Tecsmith/vr61-keyboard-pcb/docs/ref_pcb_dims/GH60_dims.png

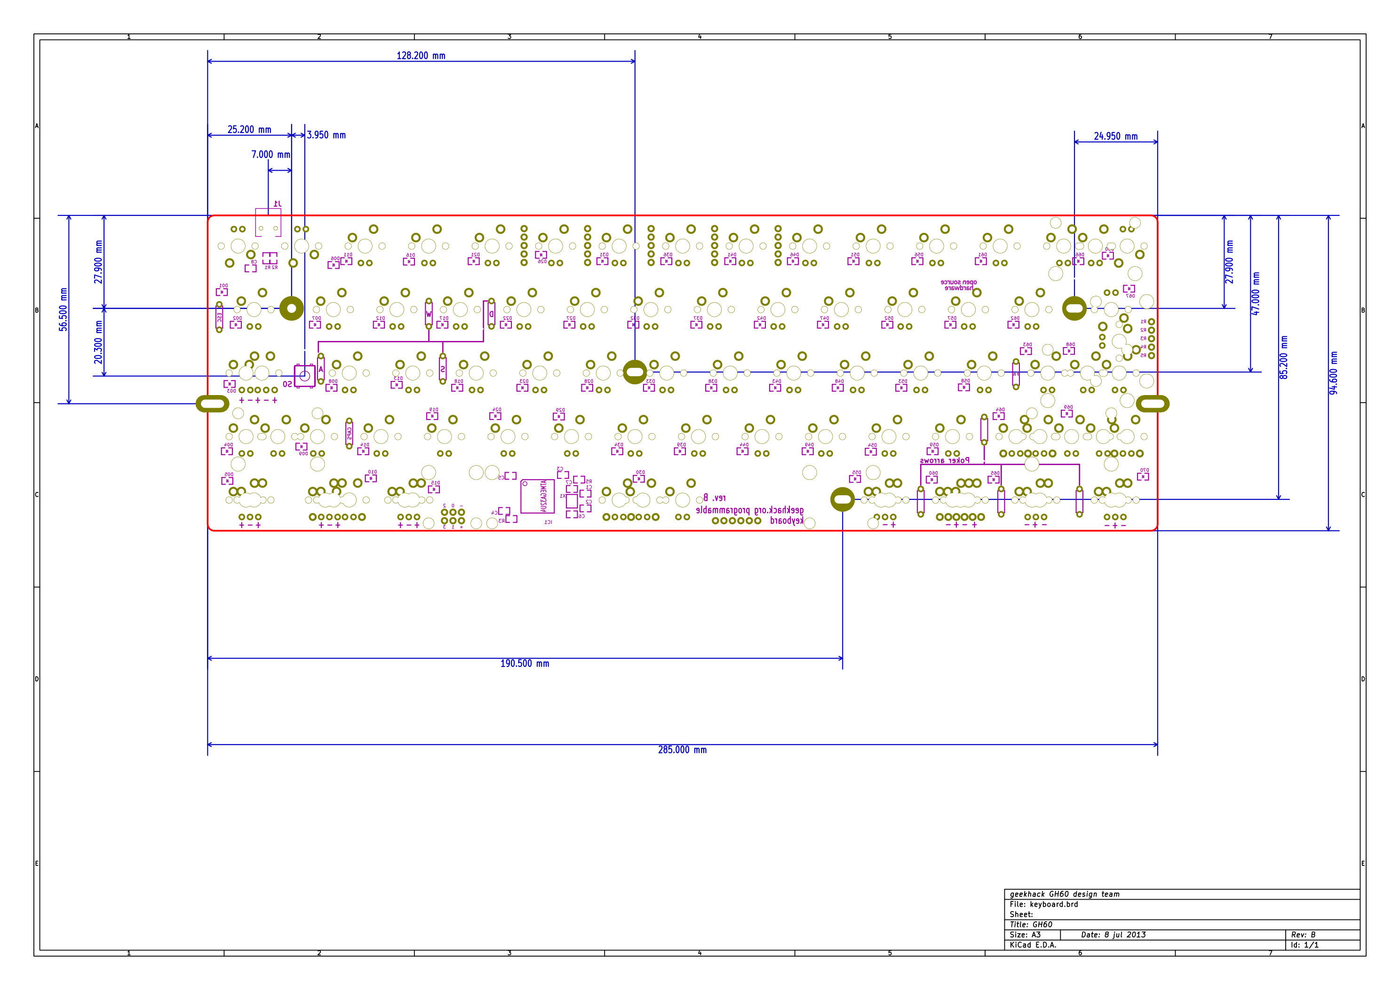
docs/ref_pcb_dims/GH60_dims.png
