Tecsmith/vr61-keyboard-pcb/docs/ref_pcb_dims/gh_60_dimensions.png

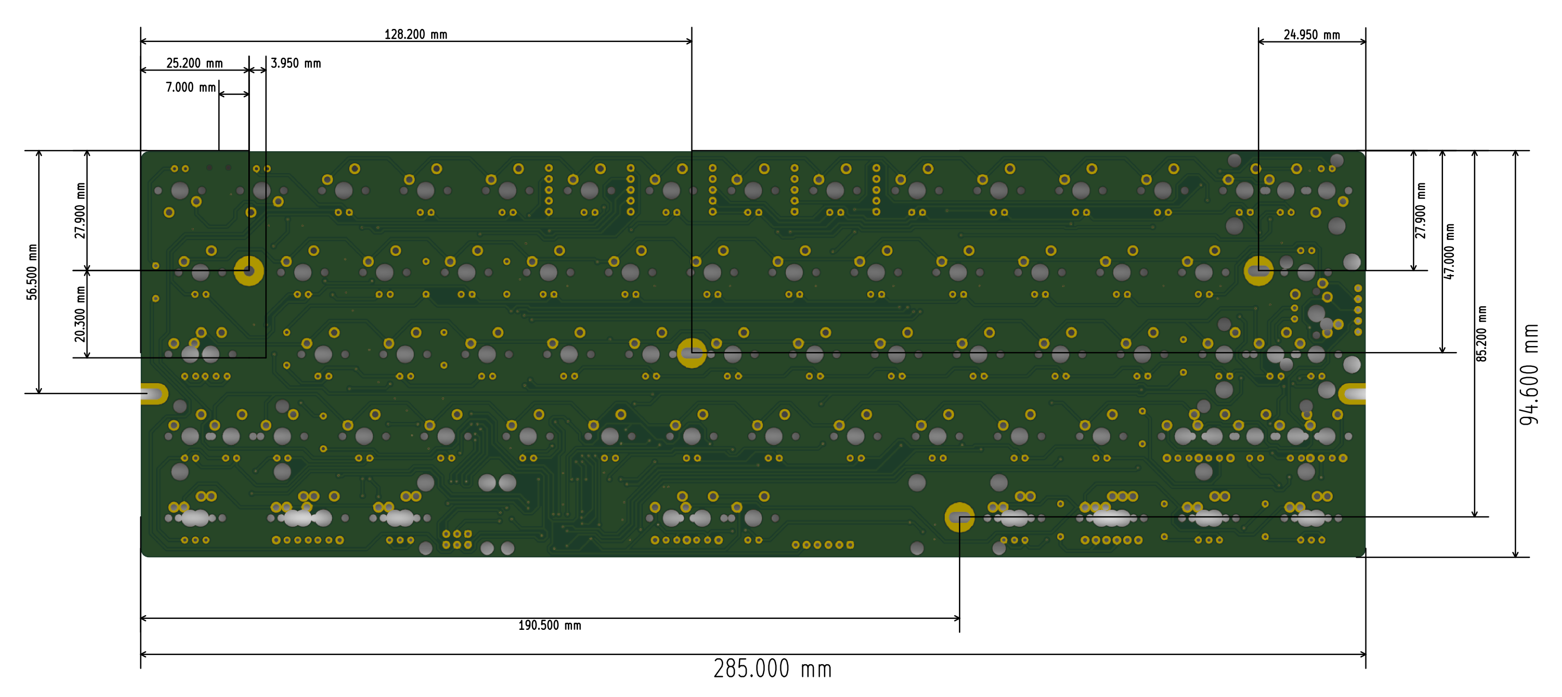
docs/ref_pcb_dims/gh_60_dimensions.png
