Tecsmith/vr61-keyboard-pcb/docs/ref_pcb_dims/mx-switch-dimension-pcb-footprint.jpg

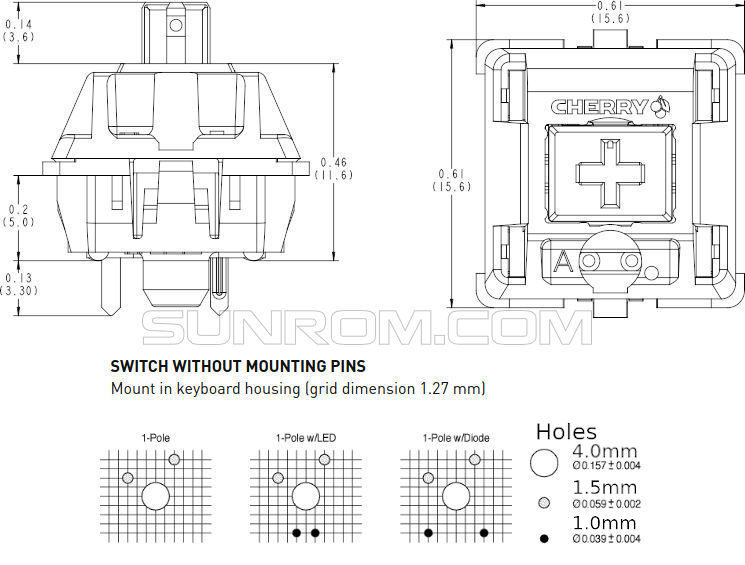
docs/ref_pcb_dims/mx-switch-dimension-pcb-footprint.jpg
