Tecsmith/vr61-keyboard-pcb/docs/ref_pcb_dims/stabilizer_attach.png

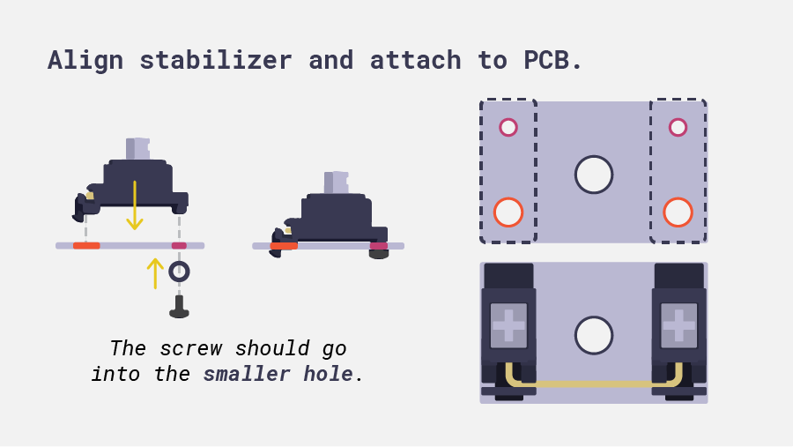
docs/ref_pcb_dims/stabilizer_attach.png
