Tecsmith/vr61-keyboard-pcb/docs/sparkfun_stm32/STM32MicroMod-GraphicalDatasheet.png

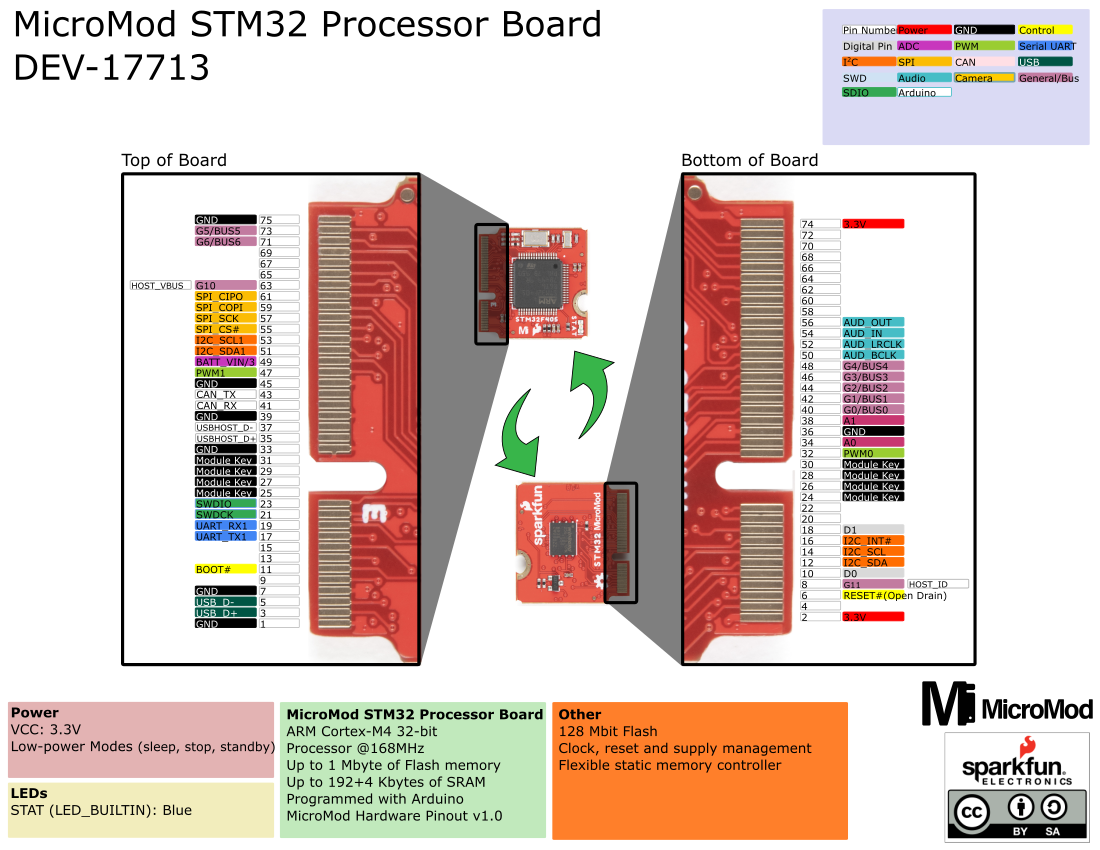
docs/sparkfun_stm32/STM32MicroMod-GraphicalDatasheet.png
