Tecsmith/vr61-keyboard-pcb/kle/vr61-micromod-poker.png

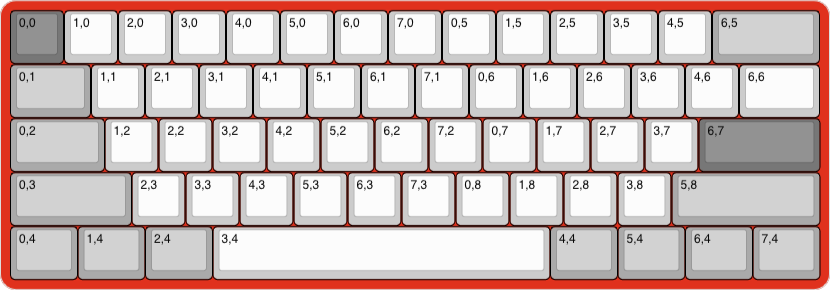
kle/vr61-micromod-poker.png
