Tecsmith/vr61-keyboard-pcb/docs/good_design_arb/3.3v protect and measure.png

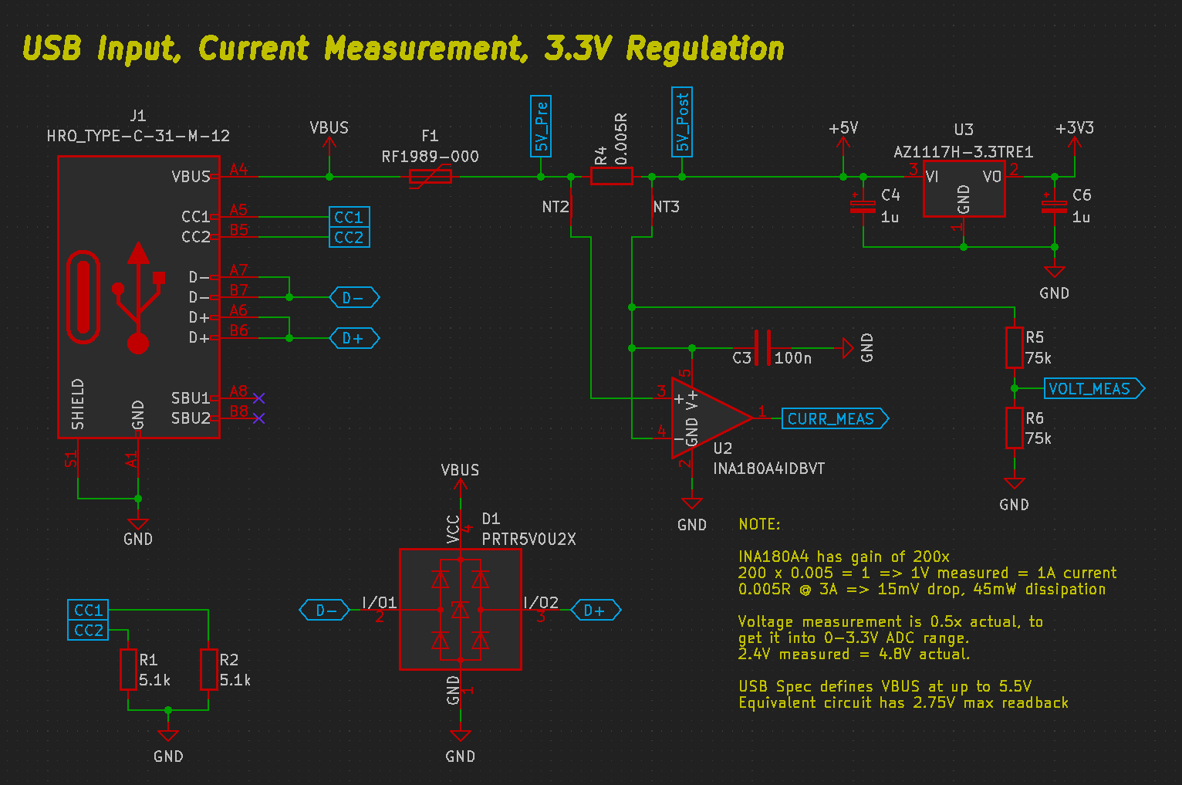
docs/good_design_arb/3.3v protect and measure.png
