Tecsmith/vr61-keyboard-pcb/docs/ref_gh60/gh60_revC_2016-06-02.pdf

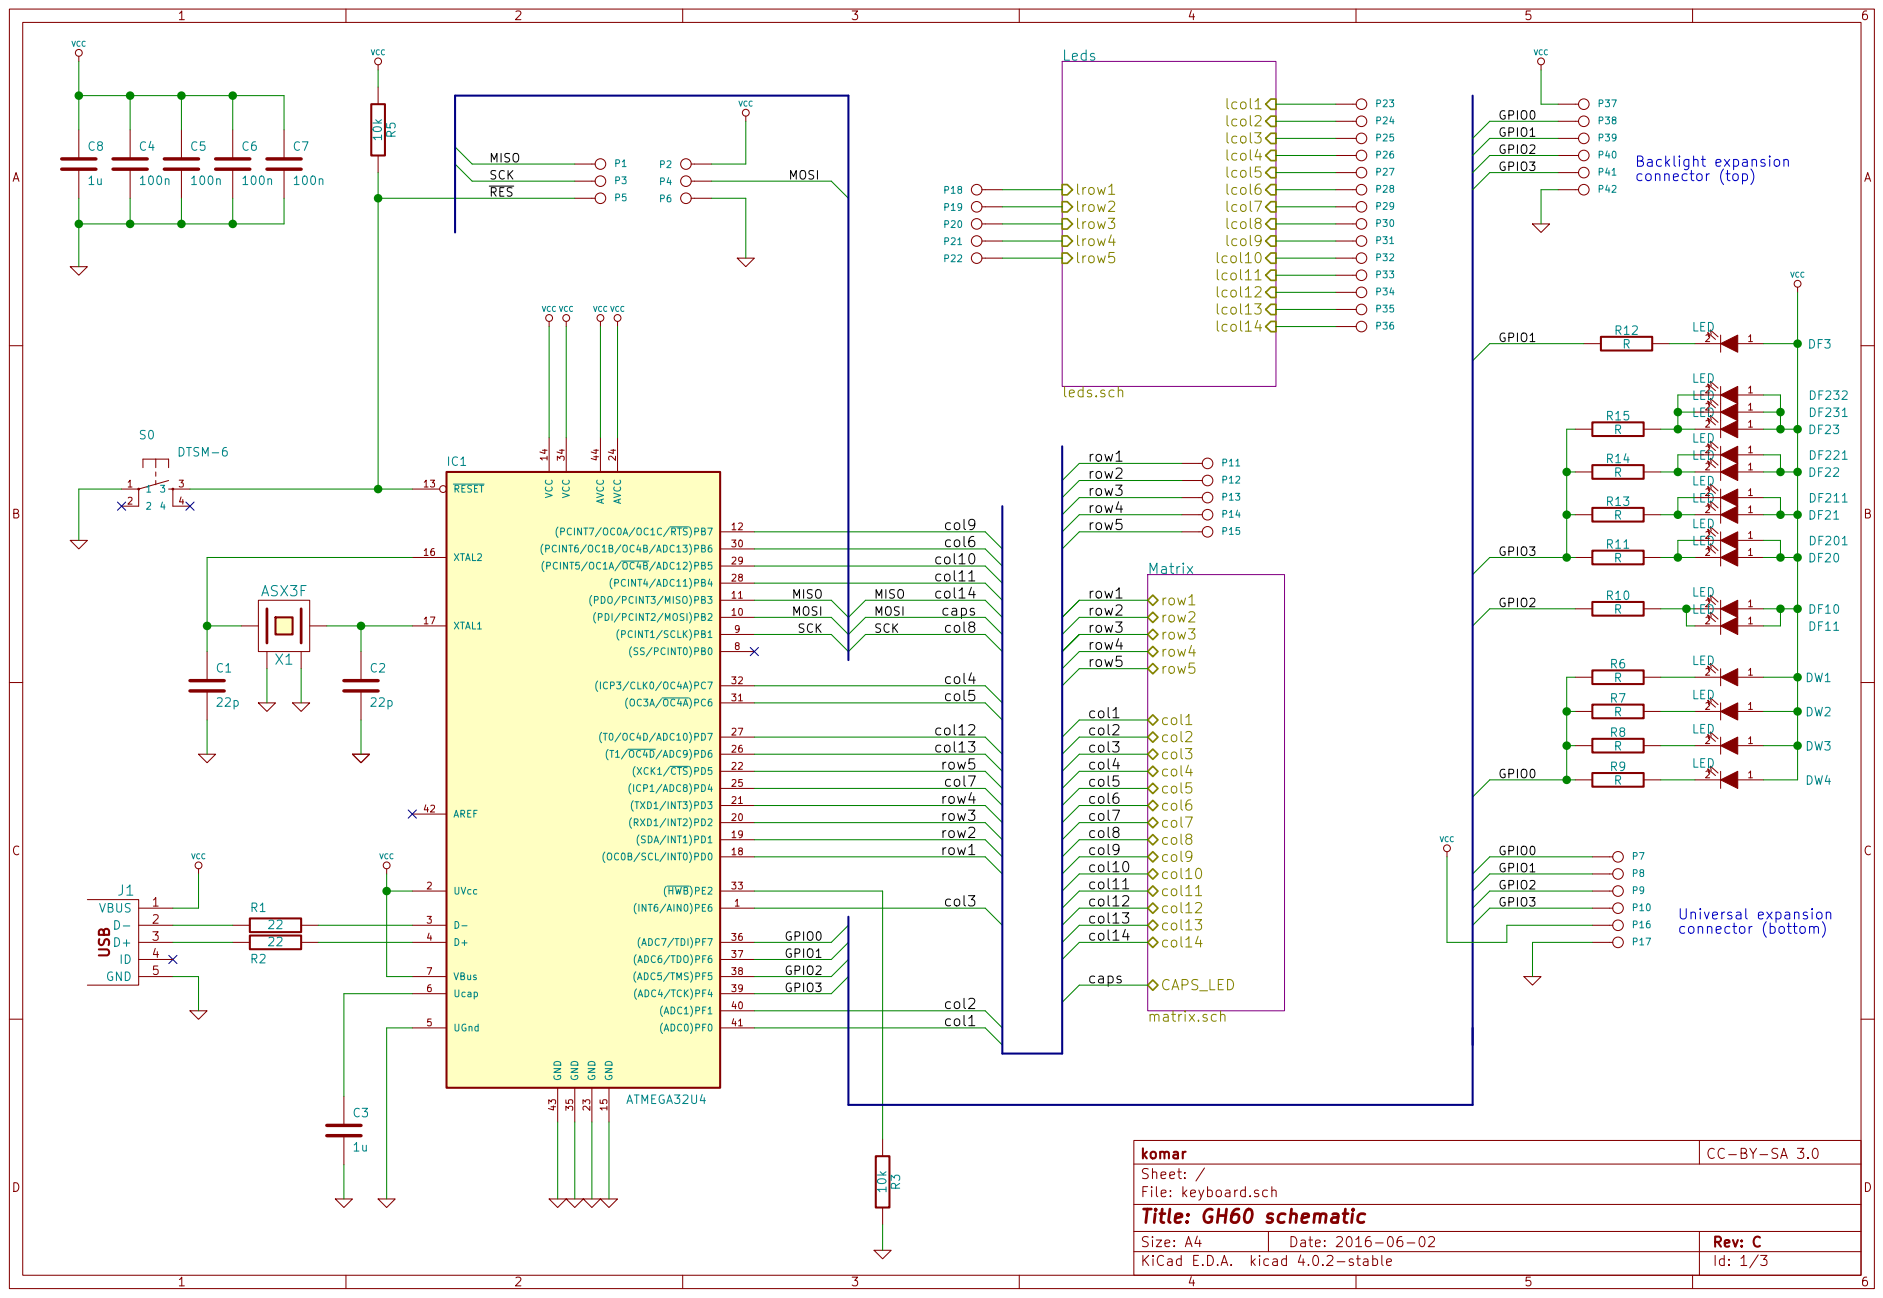
[picture p23: page 1]

File: keyboard.sch Sheet: / komar SCK MOSI MISO

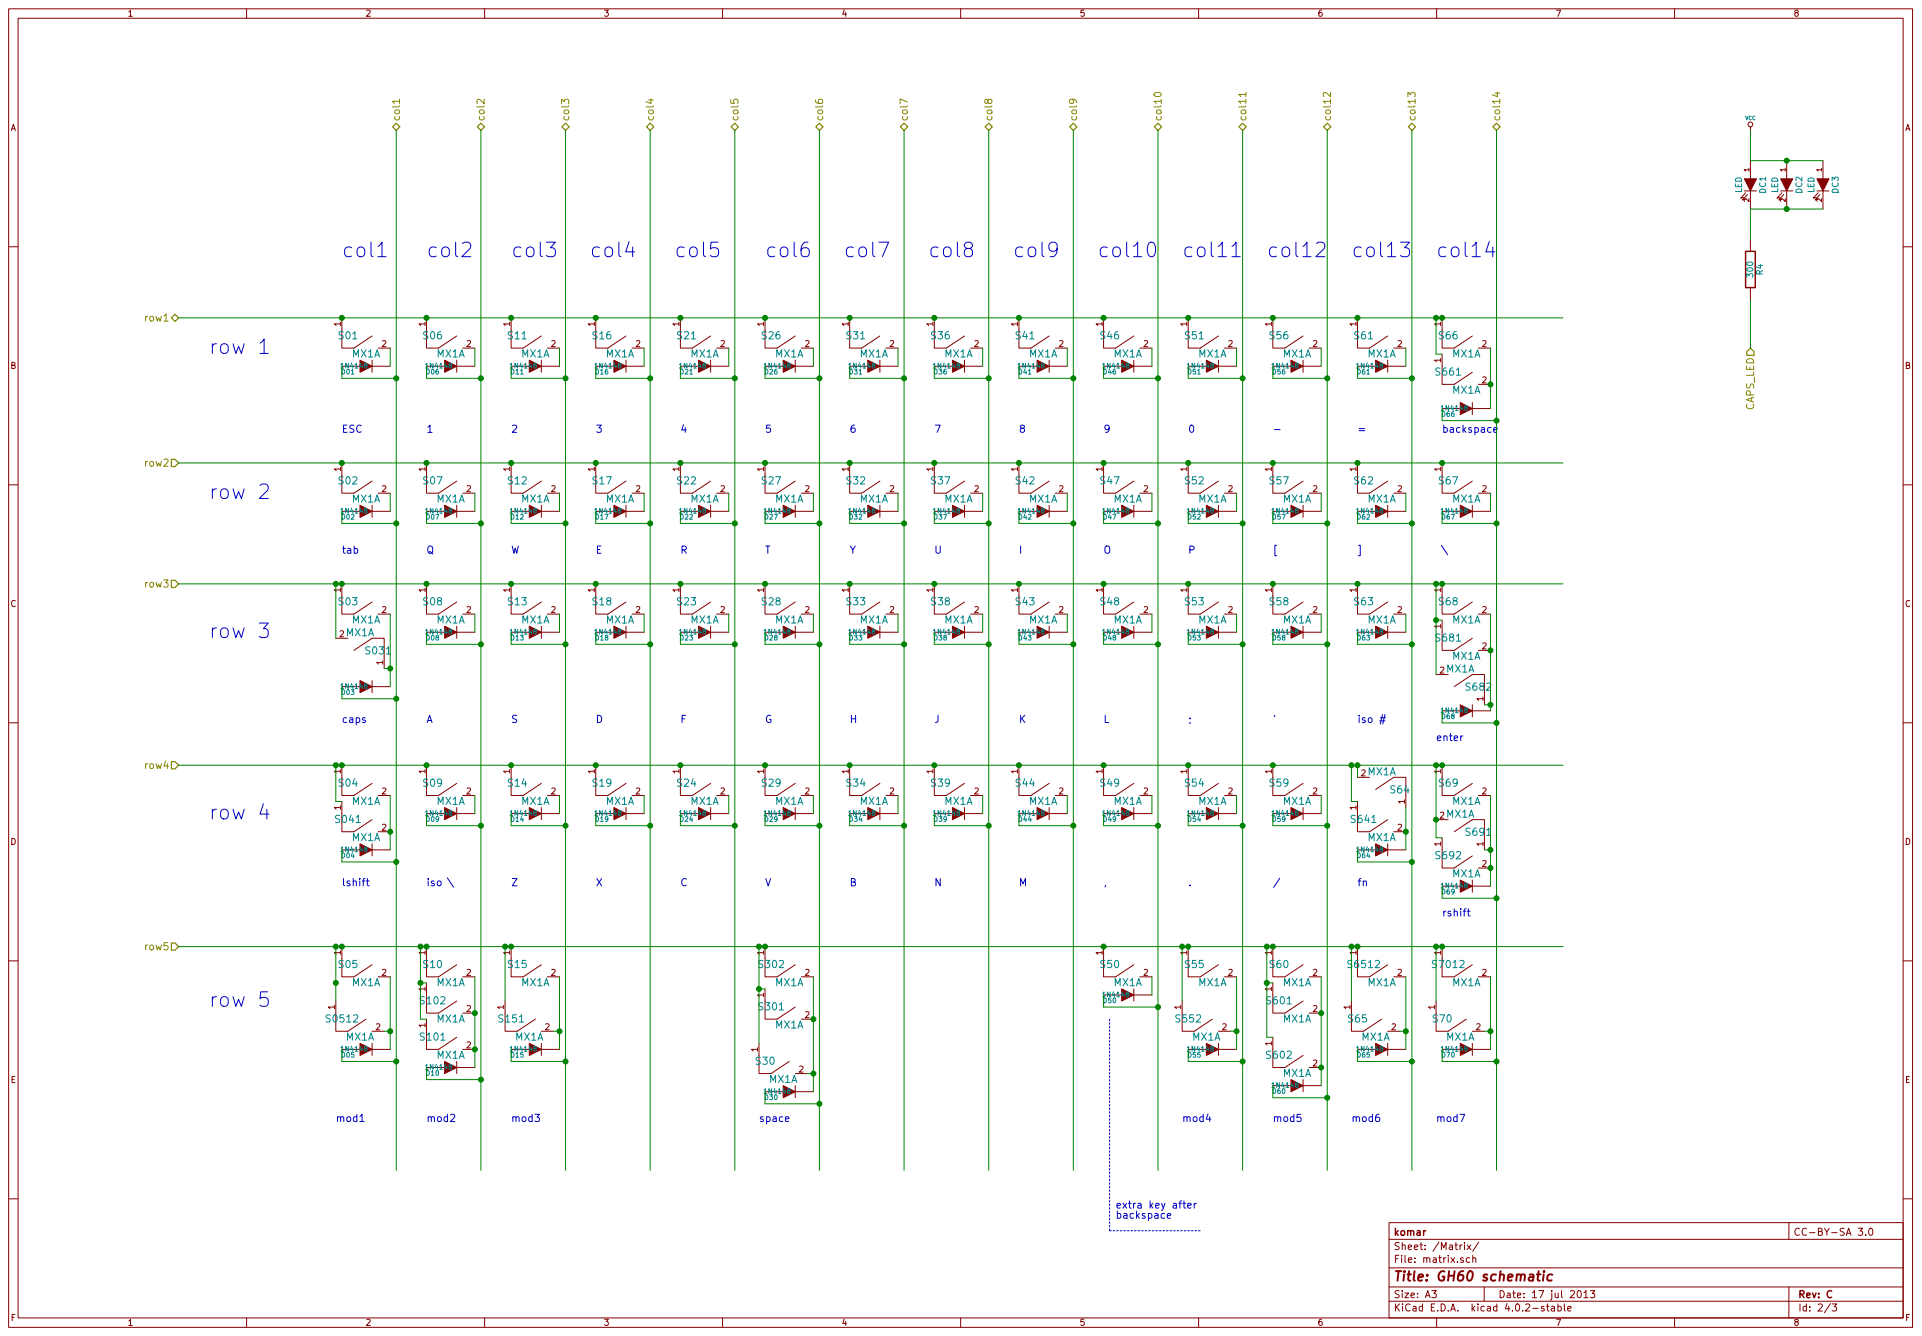
[picture p24: page 2]

File: matrix.sch Sheet: /Matrix/ komar

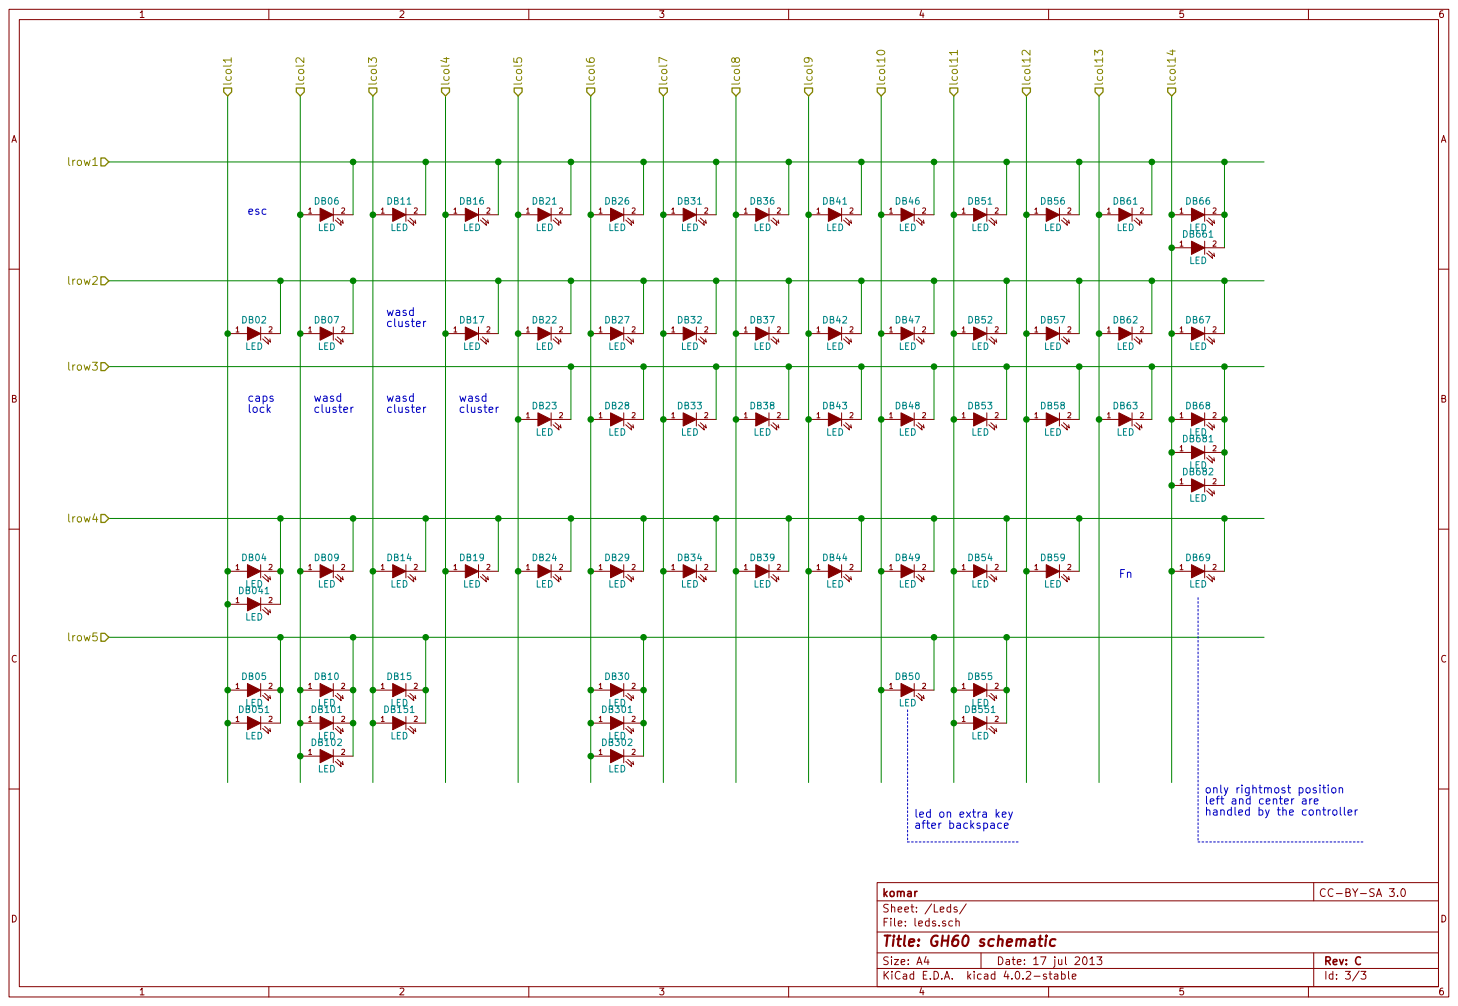
[picture p25: page 3]

only rightmost position
left and center are
handled by the controller

led on extra key

File: leds.sch Sheet: /Leds/ komar
