Tecsmith/vr61-keyboard-pcb/docs/vr61-revA.pdf

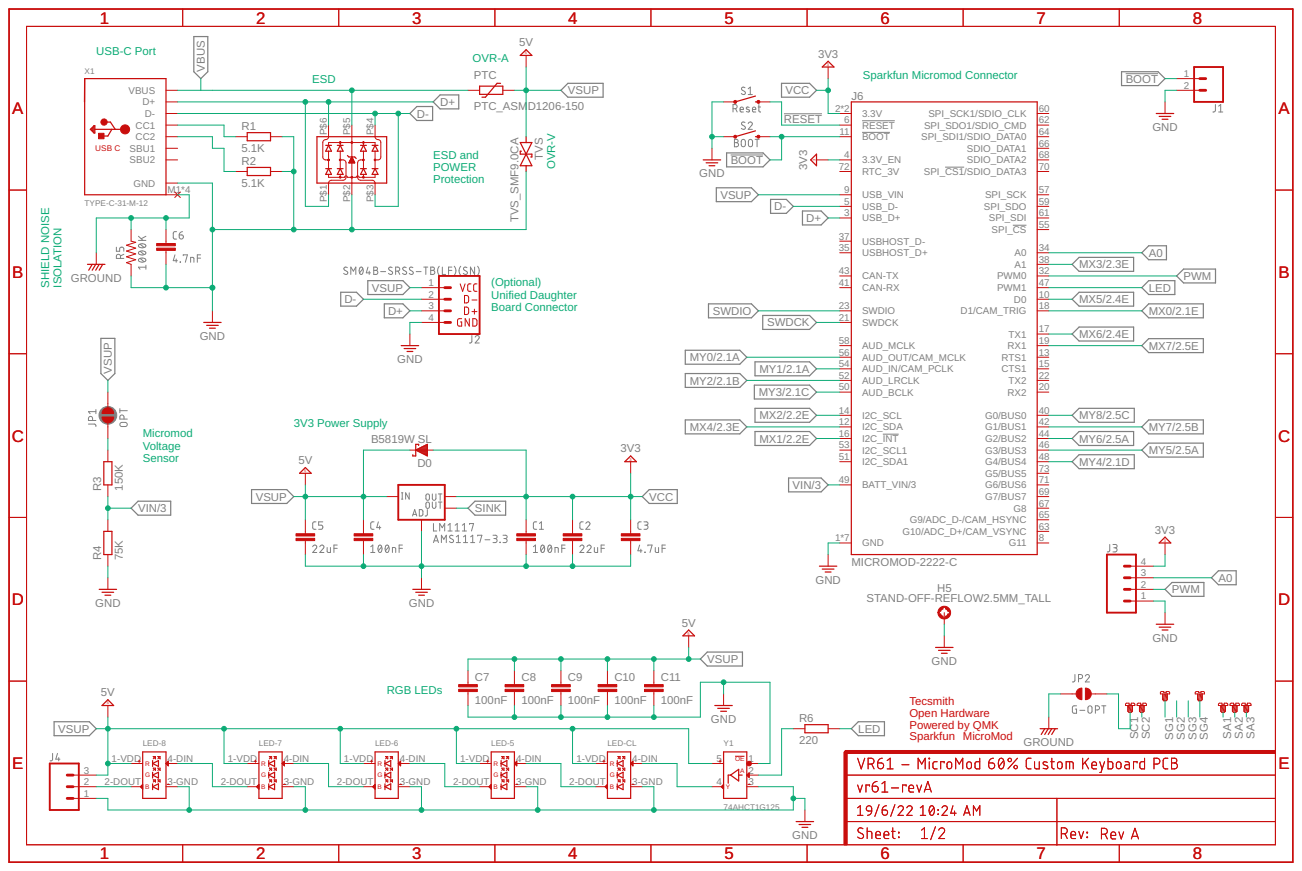
[picture p28: page 1]

(Optional)
Unified Daughter Board Connector

MX1/2.2E | I2C_SCL1 I2C_SDA1 BATT_VIN/3 | MY6/2.5A

Tecsmith
Open Hardware Sparkfun Powered by QMK

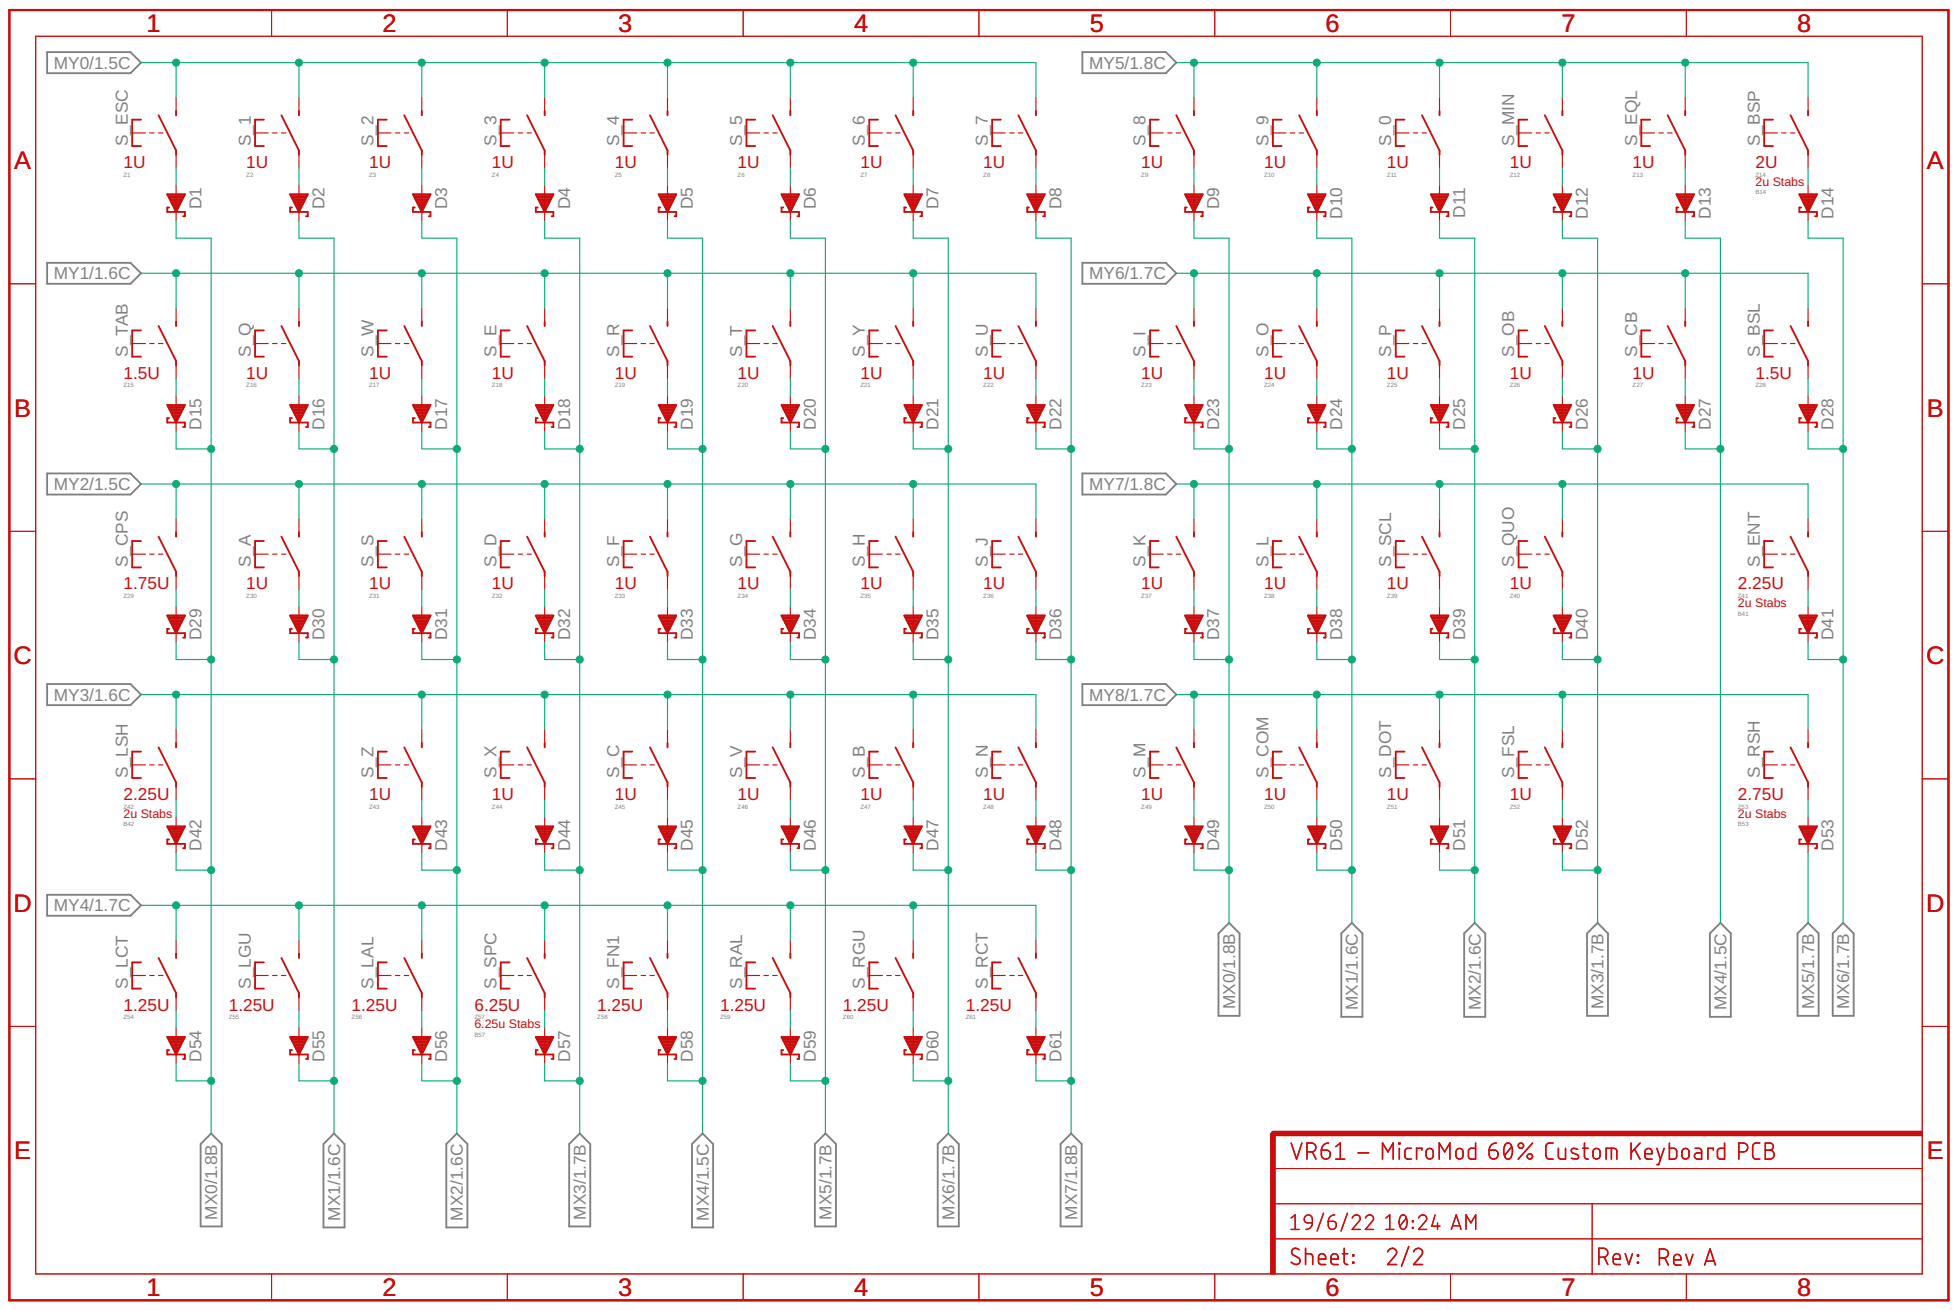
[picture p29: page 2]

S_ESC S_1 S_2 S_3 S_4 S_5 S_6 S_7 S_8 S_9 S_0 S_MIN S_EQL S_BSP D1 D2 D3 D4 D5 D6 D7 D8 D9 D10 D11 D12 D13 D14 S_TAB S_Q S_W S_E S_R S_T S_Y S_U S_I S_O S_P S_OB S_CB S_BSL D15 D16 D17 D18 D19 D20 D21 D22 D23 D24 D25 D26 D27 D28 S_CPS S_A S_S S_D S_F S_G S_H S_J S_K S_L S_SCL S_QUO S_ENT D29 D30 D31 D32 D33 D34 D35 D36 D37 D38 D39 D40 D41 S_LSH S_Z S_X S_C S_V S_B S_N S_M S_COM S_DOT S_FSL S_RSH D42 D43 D44 D45 D46 D47 D48 D49 D50 D51 D52 D53 S_LCT S_LGU S_LAL S_SPC S_FN1 S_RAL S_RGU S_RCT D54 D55 D56 D57 D58 D59 D60 D61 Z1 Z2 Z3 Z4 Z5 Z6 Z7 Z8 Z9 Z10 Z11 Z12 Z13 Z14 Z15 Z16 Z17 Z18 Z19 Z20 Z21 Z22 Z23 Z24 Z25 Z26 Z27 Z28 Z29 Z30 Z31 Z32 Z33 Z34 Z35 Z36 Z37 Z38 Z39 Z40 Z41 Z42 Z43 Z44 Z45 Z46 Z47 Z48 Z49 Z50 Z51 Z52 Z53 Z54 Z55 Z56 Z57 Z58 Z59 Z60 Z61 B14 B41 B42 B53 B57 MY0/1.5C MY1/1.6C MY2/1.5C MY3/1.6C MY4/1.7C MY5/1.8C MY6/1.7C MY7/1.8C MY8/1.7C MX5/1.7B MX5/1.7B MX6/1.7B MX6/1.7B MX7/1.8B MX0/1.8B MX0/1.8B MX1/1.6C MX1/1.6C MX2/1.6C MX2/1.6C MX3/1.7B MX3/1.7B MX4/1.5C MX4/1.5C ABCDE 1 2 3 4 5 6 7 8 ABCDE 1 2 3 4 5 6 7 8 ABCDE 1 2 3 4 5 6 7 8 ABCDE 1 2 3 4 5 6 7 8 1U 1U 1U 1U 1U 1U 1U 1U 1U 1U 1U 1U 1U 2U 1.5U 1U 1U 1U 1U 1U 1U 1U 1U 1U 1U 1U 1U 1.5U 1.75U 1U 1U 1U 1U 1U 1U 1U 1U 1U 1U 1U 2.25U 2.25U 1U 1U 1U 1U 1U 1U 1U 1U 1U 1U 2.75U 1.25U 1.25U 1.25U 6.25U 1.25U 1.25U 1.25U 1.25U 2u Stabs 2u Stabs 2u Stabs 2u Stabs 6.25u Stabs
